Blazefit/test-vial-vault/build/A_tray.scad

PART = "tray";
include <A_geom.scad>
include <../scad/vial_vault.scad>
