Blazefit/test-vial-vault/build/B_lid.scad

PART = "lid";
include <B_geom.scad>
include <../scad/vial_vault.scad>
