Blazefit/test-vial-vault/build/B_tray.scad

PART = "tray";
include <B_geom.scad>
include <../scad/vial_vault.scad>
