Blazefit/test-vial-vault/build/C_lid.scad

PART = "lid";
include <C_geom.scad>
include <../scad/vial_vault.scad>
