Blazefit/test-vial-vault/build/C_section.scad

PART="section";
include <C_geom.scad>
include <../scad/vial_vault.scad>
