Blazefit/test-vial-vault/build/C_tray.scad

PART = "tray";
include <C_geom.scad>
include <../scad/vial_vault.scad>
